TWilmer/targetboard/workspace/targetboard/inc/app_usbd_cfg.h

/*
 * @brief Configuration file needed for USB ROM stack based applications.
 *
 * @note
 * Copyright(C) NXP Semiconductors, 2012
 * All rights reserved.
 *
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
 * @par
 * Permission to use, copy, modify, and distribute this software and its
 * documentation is hereby granted, under NXP Semiconductors' and its
 * licensor's relevant copyrights in the software, without fee, provided that it
 * is used in conjunction with NXP Semiconductors microcontrollers.  This
 * copyright, permission, and disclaimer notice must appear in all copies of
 * this code.
 */
#include "lpc_types.h"
#include "error.h"
#include "usbd_rom_api.h"

#ifndef __APP_USB_CFG_H_
#define __APP_USB_CFG_H_

#ifdef __cplusplus
extern "C"
{
#endif

/** @ingroup EXAMPLES_USBDLIB_17XX40XX_CDC_UART
 * @{
 */

/* Manifest constants used by USBD LIB stack. These values SHOULD NOT BE CHANGED
   for advance features which require usage of USB_CORE_CTRL_T structure.
   Since these are the values used for compiling USB stack.
 */
#define USB_MAX_IF_NUM          8		/*!< Max interface number used for building USBDL_Lib. DON'T CHANGE. */
#define USB_MAX_EP_NUM          16		/*!< Max number of EP used for building USBD_Lib. DON'T CHANGE. */
#define USB_MAX_PACKET0         64		/*!< Max EP0 packet size used for building USBD_Lib. DON'T CHANGE. */
#define USB_FS_MAX_BULK_PACKET  64		/*!< MAXP for FS bulk EPs used for building USBD_Lib. DON'T CHANGE. */
#define USB_HS_MAX_BULK_PACKET  512		/*!< MAXP for HS bulk EPs used for building USBD_Lib. DON'T CHANGE. */
#define USB_DFU_XFER_SIZE       2048	/*!< Max DFU transfer size used for building USBD_Lib. DON'T CHANGE. */

/* Manifest constants defining interface numbers and endpoints used by a
   particular interface in this application.
 */
#define USB_CDC1_CIF_NUM         0
#define USB_CDC1_DIF_NUM         1
#define USB_CDC2_CIF_NUM         2
#define USB_CDC2_DIF_NUM         3
#define USB_CDC3_CIF_NUM         4
#define USB_CDC3_DIF_NUM         5
#define USB_CDC4_DIF_NUM         6
#define USB_CDC5_DIF_NUM         7

#define USB_CDC1_IN_EP           0x82
#define USB_CDC1_OUT_EP          0x02
#define USB_CDC1_INT_EP          0x81

#define USB_CDC2_INT_EP          0x84
#define USB_CDC2_IN_EP           0x85
#define USB_CDC2_OUT_EP          0x05

#define USB_CDC3_INT_EP          0x87
#define USB_CDC3_IN_EP           0x88
#define USB_CDC3_OUT_EP          0x08


#define USB_CDC4_IN_EP           0x8B
#define USB_CDC4_OUT_EP          0x0B


#define USB_CDC5_IN_EP           0x8E
#define USB_CDC5_OUT_EP          0x0E




/* The following manifest constants are used to define this memory area to be used
   by USBD_LIB stack.
 */
#if defined(CHIP_LPC175X_6X)
#define USB_STACK_MEM_BASE      0x2007C000
#else
#define USB_STACK_MEM_BASE      0x20000000
#endif
#define USB_STACK_MEM_SIZE      0x0800

/* USB descriptor arrays defined *_desc.c file */
extern const uint8_t USB_DeviceDescriptor[];
extern uint8_t USB_FsConfigDescriptor[];
extern const uint8_t USB_StringDescriptor[];
extern const uint8_t USB_DeviceQualifier[];

/**
 * @brief	Find the address of interface descriptor for given class type.
 * @param	pDesc		: Pointer to configuration descriptor in which the desired class
 *			interface descriptor to be found.
 * @param	intfClass	: Interface class type to be searched.
 * @return	If found returns the address of requested interface else returns NULL.
 */
extern USB_INTERFACE_DESCRIPTOR *find_IntfDesc(const uint8_t *pDesc, uint32_t intfClass, int occ);

/**
 * @}
 */

#ifdef __cplusplus
}
#endif

#endif /* __APP_USB_CFG_H_ */
