TWilmer/targetboard/workspace/targetboard/inc/twican.h

/*
 * twican.h
 *
 *  Created on: 26-Jul-2015
 *      Author: thorsten
 */

#ifndef INC_TWICAN_H_
#define INC_TWICAN_H_

#define TWICAN_SET_BAUDRATE 0x42
#define TWICAN_GET_VERSION 0x43

#endif /* INC_TWICAN_H_ */
